natarii/MegaGRRL_Desktop/sch_png/sch_1_power_supply.png

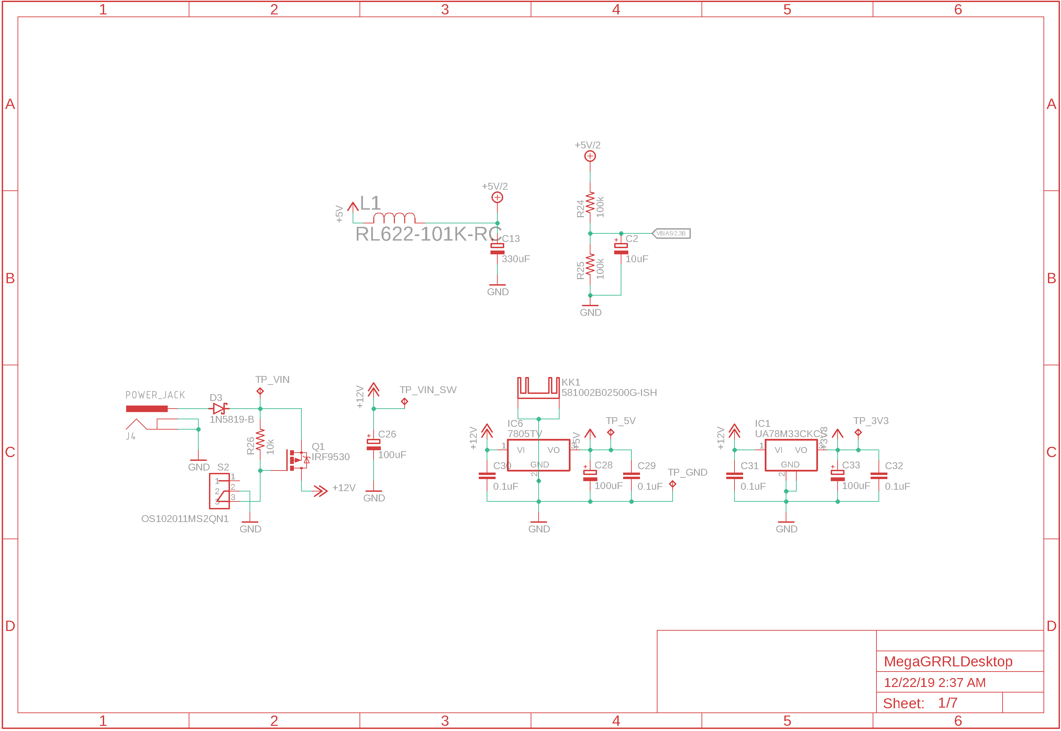
sch_png/sch_1_power_supply.png
