natarii/MegaGRRL_Desktop/sch_png/sch_3_mcu_interface.png

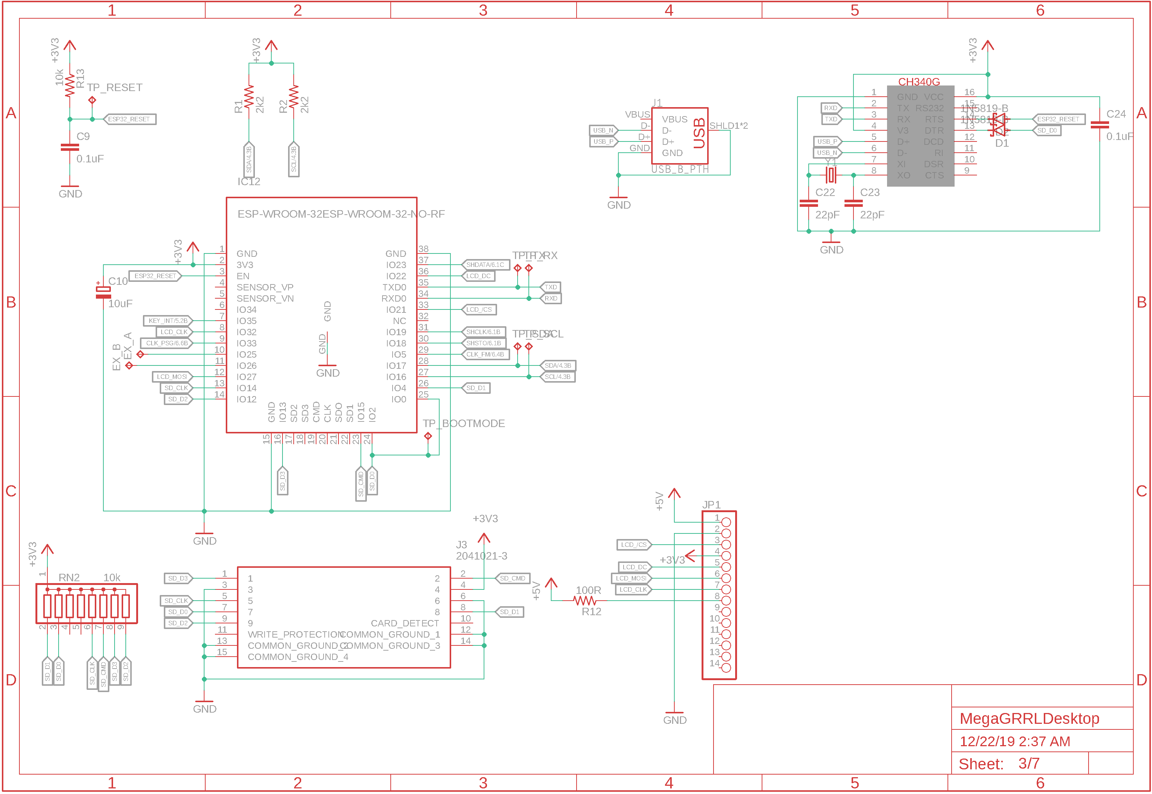
sch_png/sch_3_mcu_interface.png
