natarii/MegaGRRL_Desktop/sch_png/sch_5_keys.png

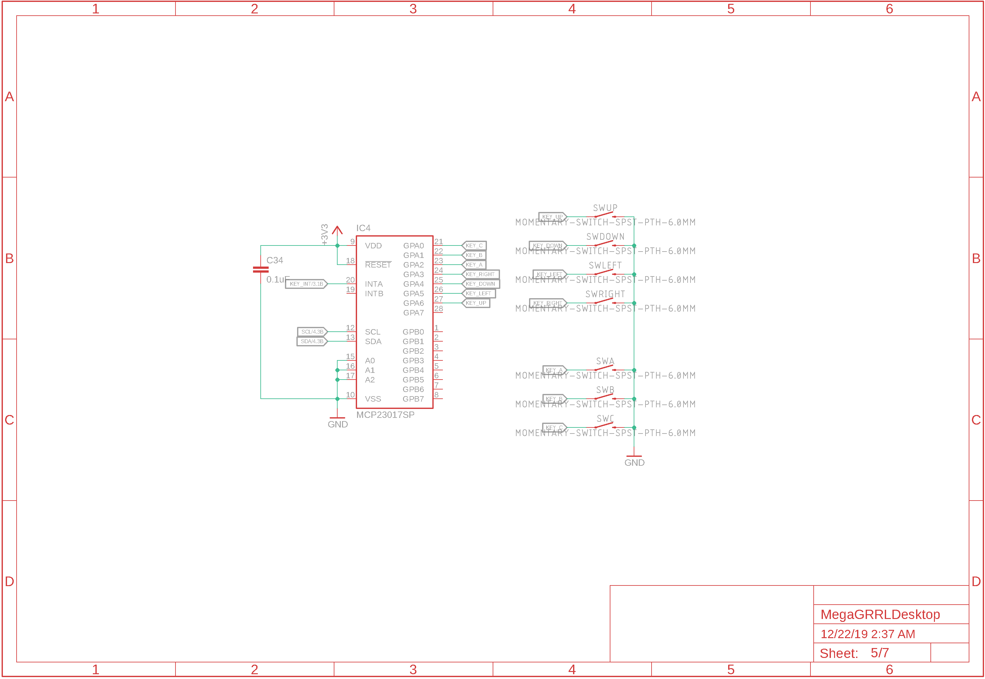
sch_png/sch_5_keys.png
